nppc/B-uOSD/Images/E010S_AIO_Video_Connection.jpg

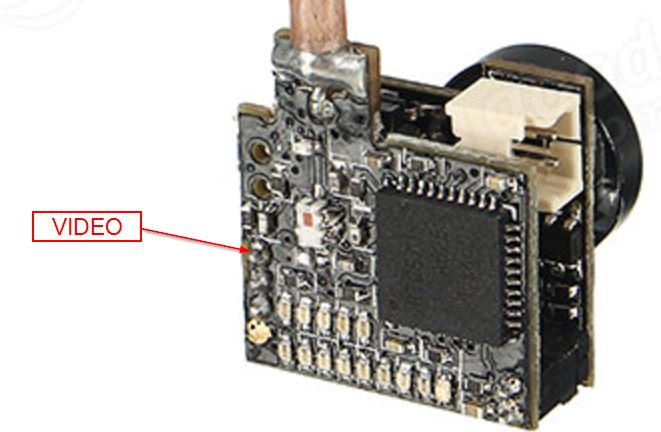
Images/E010S_AIO_Video_Connection.jpg
