nppc/B-uOSD/Images/Sample_DC_2LINES_combined.jpg

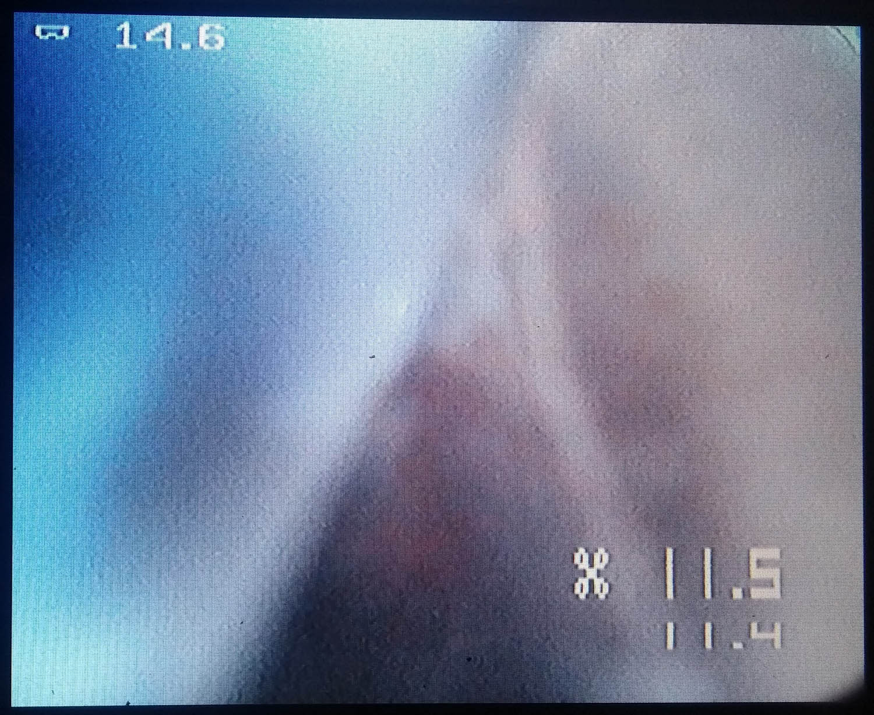
Images/Sample_DC_2LINES_combined.jpg
