nppc/B-uOSD/Refs/Timing_PAL_FrameSignal.gif

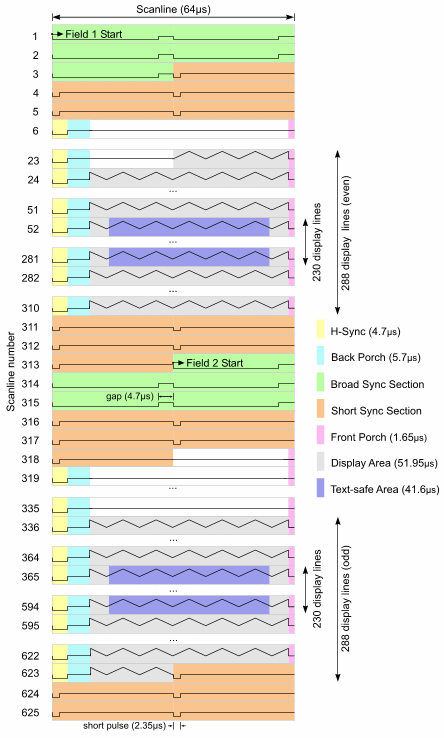
Refs/Timing_PAL_FrameSignal.gif
